DL9AS/Minimal-APRS-TX/Software/Source-Code/aprs.cpp

/*
 * This file is part of the Minimal APRS TX project.
 * 
 
 * Copyright (C) 2023  Amon Schumann / DL9AS
 
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
 * You should have received a copy of the GNU General Public License
 * along with this program. If not, see <http://www.gnu.org/licenses/>.
 */ 

#include <Arduino.h>
#include <SPI.h>

#include "aprs.h"
#include "globals.h"
#include "SX1278.h"
#include "ax25.h"
#include "config.h"

// Exported functions
void aprs_send_position_packet(uint64_t *freq, uint8_t pwr, uint32_t deviation, char *src_call, uint8_t src_SSID, char *digi_call, uint8_t digi_SSID, char symbol, char symbol_overlay, char *latitude, char *longitude, char *info, char *comment) 
{
  SX1278_begin();
  SX1278_enable_TX_direct(freq, pwr, deviation);
  
  // Send flag often times at start
  ax25_TX_flag(APRS_FLAGS_AT_BEGINNING);

  continuous_crc = 0xFFFF; // Set CRC at start to 0xFFFF, this is standard in AX25
  
  // Send destination callsign [6 bytes Call][1 byte SSID] and left shifted by 1
  char buf[8];
  sprintf(buf, "%-6s%c", APRS_DESTINATION_CALLSIGN, APRS_DESTINATION_SSID);
  for(uint8_t i = 0; i < 7; i++) ax25_TX_byte(buf[i] << 1, false);
  
  // Send source callsign [6 bytes Call][1 byte SSID] and left shifted by 1
  sprintf(buf, "%-6s%c", src_call, src_SSID);
  for(uint8_t i = 0; i < 7; i++) ax25_TX_byte(buf[i] << 1, false);
  
  // Send digipeater callsign [6 bytes Call][1 byte SSID], left shifted by 1 and SSID + 1
  sprintf(buf, "%-6s%c", digi_call, digi_SSID);
  for(uint8_t i = 0; i < 6; i++) ax25_TX_byte(buf[i] << 1, false);
  ax25_TX_byte((buf[6]  << 1) + 1, HIGH); // Digieater SSID also + 1 after left shift
  
  // Send control field and protocol field
  ax25_TX_byte(0x03, false);
  ax25_TX_byte(0xf0, false);

  // Send '!' for uncompressed position packet
  ax25_TX_byte('!', false);
  
  // Send latitude
  ax25_TX_c_string(latitude, 8);

  // Send symbol table id
  ax25_TX_byte(symbol_overlay, false);

  // Send latitude
  ax25_TX_c_string(longitude, 9);

  // Send symbol code
  ax25_TX_byte(symbol, false);

  // Send info
  ax25_TX_c_string(info, strlen(info));

  // Send comment
  ax25_TX_c_string(comment, strlen(comment));

  // Send CRC LSB and MSB
  byte crc_lsb = continuous_crc;
  byte crc_msb = continuous_crc >> 8;
  ax25_TX_byte(crc_lsb ^ 0xFF, false);
  ax25_TX_byte(crc_msb ^ 0xFF, false);

  // Send flag at end
  ax25_TX_flag(3);

  SX1278_sleep();
}

void aprs_send_status_packet(uint64_t *freq, uint8_t pwr, uint32_t deviation, char *src_call, uint8_t src_SSID, char *digi_call, uint8_t digi_SSID, char *info, char *comment) 
{
  SX1278_begin();
  SX1278_enable_TX_direct(freq, pwr, deviation);
  
  // Send flag often times at start
  ax25_TX_flag(APRS_FLAGS_AT_BEGINNING);

  continuous_crc = 0xFFFF; // Set CRC at start to 0xFFFF, this is standard in AX25
  
  // Send destination callsign [6 bytes Call][1 byte SSID] and left shifted by 1
  char buf[8];
  sprintf(buf, "%-6s%c", APRS_DESTINATION_CALLSIGN, APRS_DESTINATION_SSID);
  for(uint8_t i = 0; i < 7; i++) ax25_TX_byte(buf[i] << 1, false);
  
  // Send source callsign [6 bytes Call][1 byte SSID] and left shifted by 1
  sprintf(buf, "%-6s%c", src_call, src_SSID);
  for(uint8_t i = 0; i < 7; i++) ax25_TX_byte(buf[i] << 1, false);
  
  // Send digipeater callsign [6 bytes Call][1 byte SSID], left shifted by 1 and SSID + 1
  sprintf(buf, "%-6s%c", digi_call, digi_SSID);
  for(uint8_t i = 0; i < 6; i++) ax25_TX_byte(buf[i] << 1, false);
  ax25_TX_byte((buf[6]  << 1) + 1, HIGH); // Digieater SSID also + 1 after left shift
  
  // Send control field and protocol field
  ax25_TX_byte(0x03, false);
  ax25_TX_byte(0xf0, false);

  // Send '>' for status packet
  ax25_TX_byte('>', false);
  
  // Send info
  ax25_TX_c_string(info, strlen(info));

  // Send comment
  ax25_TX_c_string(comment, strlen(comment));

  // Send CRC LSB and MSB
  byte crc_lsb = continuous_crc;
  byte crc_msb = continuous_crc >> 8;
  ax25_TX_byte(crc_lsb ^ 0xFF, false);
  ax25_TX_byte(crc_msb ^ 0xFF, false);

  // Send flag at end
  ax25_TX_flag(3);

  SX1278_sleep();
}
